extinct00/EagleV1/PCB/EagleV1/cesky_lev_gpt.png

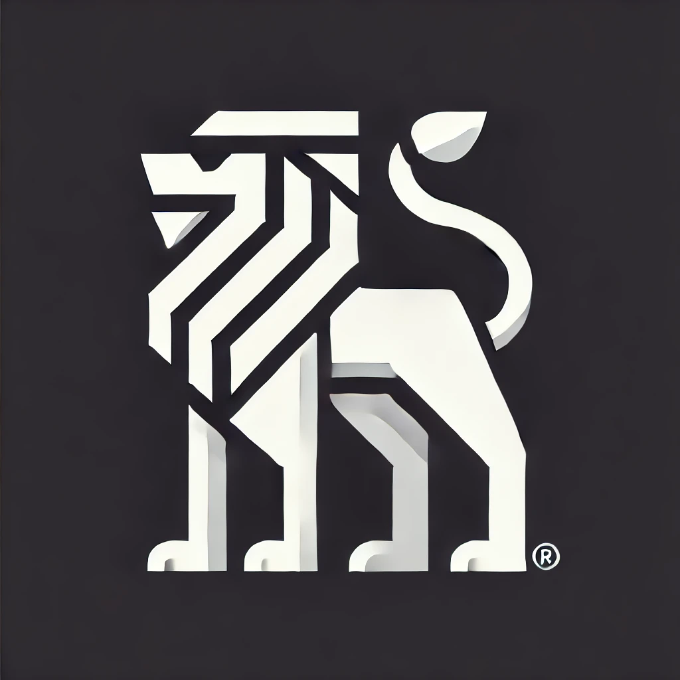
PCB/EagleV1/cesky_lev_gpt.png
